pilotman695/compact_LTM4607_PCB/sch/carrier/4418.asc

C1: cap; 1n
C2: cap; 100n
C3: cap; 100µ; Rser=63m
C4: cap; 540µ; Rser=10m
C5: cap; 100n
C6: cap; 100n
Q1: pmos; HAT1072H
Q2: pmos; HAT1072H
Q3: pmos; HAT1072H
Q4: pmos; HAT1072H
R1: res; 150k
R2: res; 210k
R3: res; 4.12Meg
R4: res; 150k
R5: res; 210k
R6: res; 4.12Meg
R7: res; 255k
R8: res; 100k
R9: res; 100k
R10: res; 1
R11: res; 30m
R12: res; 1k
R13: res; 1k
U1: LTC4418
V1: voltage; PULSE(0 16.8 3 1 10 1 3 5); Rser=10m
V2: voltage; 19.4; Rser=10m
Named nets: 0
.tran 30 uic
