pilotman695/compact_LTM4607_PCB/sch/converter/v2/compact_converter_12.asc

C2: cap; .002µ
C3: cap; 0p
Cinb1: cap; 180µ; x1; Rser=21m
Cob1: cap; 220µ; x2; Rser=21m
Coc1: cap; 8µ; Rser=2.3m Lser=1.14n
Coc2: cap; 8µ; Rser=2.3m Lser=1.14n
Coc3: cap; 8µ; Rser=2.3m Lser=1.14n
Coc4: cap; 8µ; Rser=2.3m Lser=1.14n
Coc5: cap; 8µ; Rser=2.3m Lser=1.14n
L1: PA4343.682ANL
R1: res; 2400k
R2: res; 4.7k
R3: res; 100K
R4: res; 2.7k
RfbBot1: res; 7.13k
Rsense1: res; 7.5m
U1: LTM4607
Vin1: voltage; 24; Rser=5m
Named nets: 0, IN, OUT
.tran 0 150m 95m startup
