pilotman695/compact_LTM4607_PCB/sch/converter/v2/compact_converter_24.asc

C2: cap; .002µ
C3: cap; 0p
Cinb1: cap; 330µ; x1; Rser=21m
Cob1: cap; 330µ; x1; Rser=21m
Coc1: cap; 8µ; Rser=2.3m Lser=1.14n
Coc2: cap; 8µ; Rser=2.3m Lser=1.14n
Coc3: cap; 8µ; Rser=2.3m Lser=1.14n
Coc4: cap; 8µ; Rser=2.3m Lser=1.14n
Coc5: cap; 8µ; Rser=2.3m Lser=1.14n
Coc6: cap; 8µ; Rser=2.3m Lser=1.14n
Lo1: ind; 4.7µ; Rser=8m
R1: res; 4.8
R2: res; 4.7k
R3: res; 100K
R4: res; 2.7k
RfbBot1: res; 3.4k
Rsense1: res; 7.5m
U1: LTM4607
Vin1: voltage; 15; Rser=5m
Named nets: 0, IN, OUT
.tran 0 150m 95m startup
